qbancoffee/cocoplusplus/3d_models/EG1213.stp

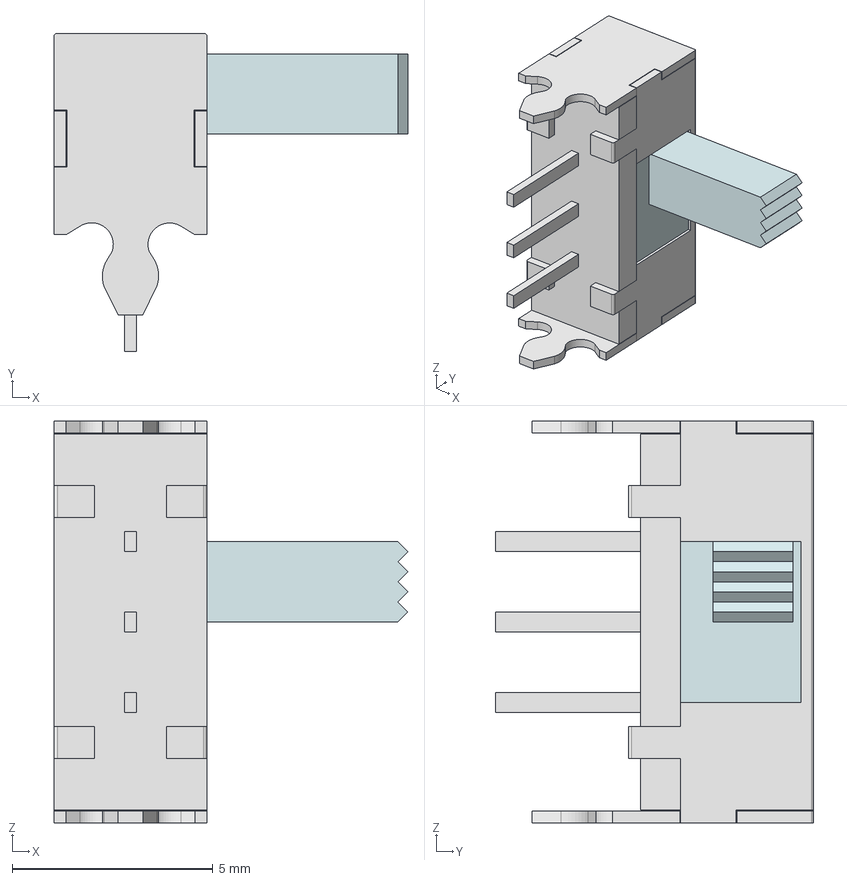
[picture p15: CAD file, 2021-08-31]
3d_models/EG1213.stp
8.80 x 7.90 x 10.0 mm
EG1213 SHELL
EG1213 TERM
EG1213 ACTUATOR
