qbancoffee/cocoplusplus/3d_models/009652038.stp

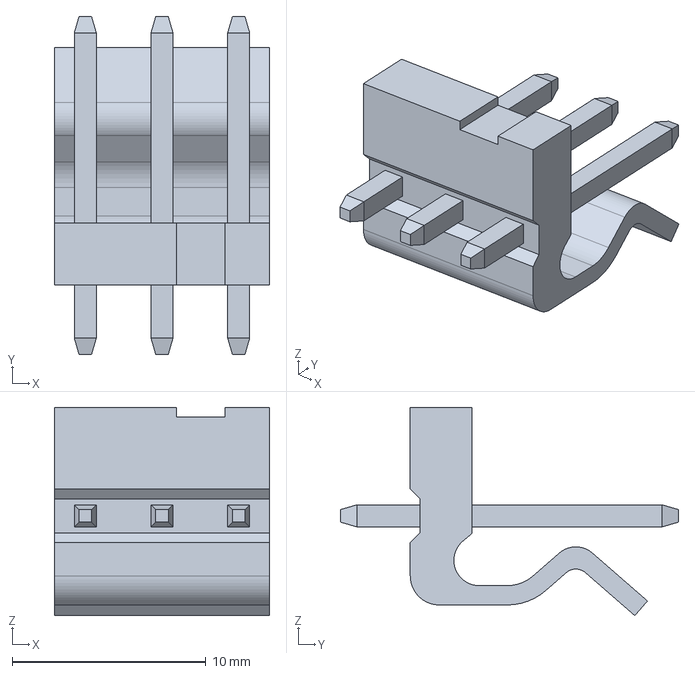
[picture p16: CAD file, 2021-08-31]
3d_models/009652038.stp
11.1 x 17.4 x 10.8 mm
